ForestKatsch/unofficial-tesla-seat-controller/firmware/switchpack_states.h

#include <stdint.h>
const uint8_t switchpack_states[1024] = {
    0b0000, 0b0000, 0b0000, 0b0000, 0b0000, 0b0000, 0b0000, 0b0000, 0b0000,
    0b0000, 0b0000, 0b0000, 0b0000, 0b0000, 0b0000, 0b0000, 0b0000, 0b0000,
    0b0000, 0b0000, 0b0000, 0b0000, 0b0000, 0b0000, 0b0000, 0b0000, 0b0000,
    0b0000, 0b0000, 0b0000, 0b0000, 0b0000, 0b0000, 0b0000, 0b0000, 0b0000,
    0b0000, 0b0000, 0b0000, 0b0000, 0b0000, 0b0000, 0b0000, 0b0000, 0b0000,
    0b0000, 0b0000, 0b0000, 0b0000, 0b0000, 0b0000, 0b0000, 0b0000, 0b0000,
    0b0000, 0b0000, 0b0000, 0b0000, 0b0000, 0b0000, 0b0000, 0b0000, 0b0000,
    0b0000, 0b0000, 0b0000, 0b0000, 0b0000, 0b0000, 0b0000, 0b0000, 0b0000,
    0b0000, 0b0000, 0b0000, 0b0000, 0b0000, 0b0000, 0b0000, 0b0000, 0b0000,
    0b0000, 0b0000, 0b0000, 0b0000, 0b0000, 0b0000, 0b0000, 0b0000, 0b0000,
    0b0000, 0b0000, 0b0000, 0b0000, 0b0000, 0b0000, 0b0000, 0b0000, 0b0000,
    0b0000, 0b0000, 0b0000, 0b0000, 0b0000, 0b0000, 0b0000, 0b0000, 0b0000,
    0b0000, 0b0000, 0b0000, 0b0000, 0b0000, 0b0000, 0b0000, 0b0000, 0b0000,
    0b0000, 0b0000, 0b0000, 0b0000, 0b0000, 0b0000, 0b0000, 0b0000, 0b0000,
    0b0000, 0b0000, 0b0000, 0b0000, 0b0000, 0b0000, 0b0000, 0b0000, 0b0000,
    0b0000, 0b0000, 0b0000, 0b0000, 0b0000, 0b0000, 0b0000, 0b0000, 0b0000,
    0b0000, 0b0000, 0b0000, 0b0000, 0b0000, 0b0000, 0b0000, 0b0000, 0b0000,
    0b0000, 0b0000, 0b0000, 0b0000, 0b0000, 0b0000, 0b0000, 0b0000, 0b0000,
    0b0000, 0b0000, 0b0000, 0b0000, 0b0000, 0b0000, 0b0000, 0b0000, 0b0000,
    0b0000, 0b0000, 0b0000, 0b0000, 0b0000, 0b0000, 0b0000, 0b0000, 0b0000,
    0b0000, 0b0000, 0b0000, 0b0000, 0b0000, 0b0000, 0b0000, 0b0000, 0b0000,
    0b0000, 0b0000, 0b0000, 0b0000, 0b0000, 0b0000, 0b0000, 0b0000, 0b0000,
    0b0000, 0b0000, 0b0000, 0b0000, 0b0000, 0b0000, 0b0000, 0b0000, 0b0000,
    0b0000, 0b0000, 0b0000, 0b0000, 0b0000, 0b0000, 0b0000, 0b0000, 0b0000,
    0b0000, 0b0000, 0b0000, 0b0000, 0b0000, 0b0000, 0b0000, 0b0000, 0b0000,
    0b0000, 0b0000, 0b0000, 0b0000, 0b0000, 0b0000, 0b0000, 0b0000, 0b0000,
    0b0000, 0b0000, 0b0000, 0b0000, 0b0000, 0b0000, 0b0000, 0b0000, 0b0000,
    0b0000, 0b0000, 0b0000, 0b0000, 0b0000, 0b0000, 0b0000, 0b0000, 0b0000,
    0b0000, 0b0000, 0b0000, 0b0000, 0b0000, 0b0000, 0b0000, 0b0000, 0b0000,
    0b0000, 0b0000, 0b0000, 0b0000, 0b0000, 0b0000, 0b0000, 0b0000, 0b0000,
    0b0000, 0b0000, 0b0000, 0b0000, 0b0000, 0b0000, 0b0000, 0b0000, 0b0000,
    0b0000, 0b0000, 0b0000, 0b0000, 0b0000, 0b0000, 0b0000, 0b0000, 0b0000,
    0b0000, 0b0000, 0b0000, 0b0000, 0b0000, 0b0000, 0b0000, 0b0000, 0b0000,
    0b0000, 0b0000, 0b0000, 0b0000, 0b0000, 0b0000, 0b0000, 0b0000, 0b0000,
    0b0000, 0b0000, 0b0000, 0b0000, 0b0000, 0b0000, 0b0000, 0b0000, 0b0000,
    0b0000, 0b0000, 0b0000, 0b0000, 0b0000, 0b0000, 0b0000, 0b0000, 0b0000,
    0b0000, 0b0000, 0b0000, 0b0000, 0b0000, 0b0000, 0b0000, 0b0000, 0b0000,
    0b0000, 0b0000, 0b0000, 0b0000, 0b0000, 0b0000, 0b0000, 0b0000, 0b0000,
    0b0000, 0b0000, 0b0000, 0b0000, 0b0000, 0b0000, 0b0000, 0b0000, 0b0000,
    0b0000, 0b0000, 0b0000, 0b0000, 0b0000, 0b0000, 0b0000, 0b0000, 0b0000,
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
};
